tomeucapo/atmega328trainer/src/anemometre/ds18b20.h

#ifndef DS18B20_H
#define DS18B20_H
#define DS18B20_ERROR_TEMP (-127.0f)

#define DS18B20_CONFIG 0x1F  // resolucion 9-bit (0.5 C, ~94 ms)
#define DS18B20_CONV_MS 100

void ds18b20_init(void);
float ds18b20_get_temp(void);

#endif
